ihartwig/mate-net-monitor/pcb/gerber/mate-net-monitor-Fab.pdf

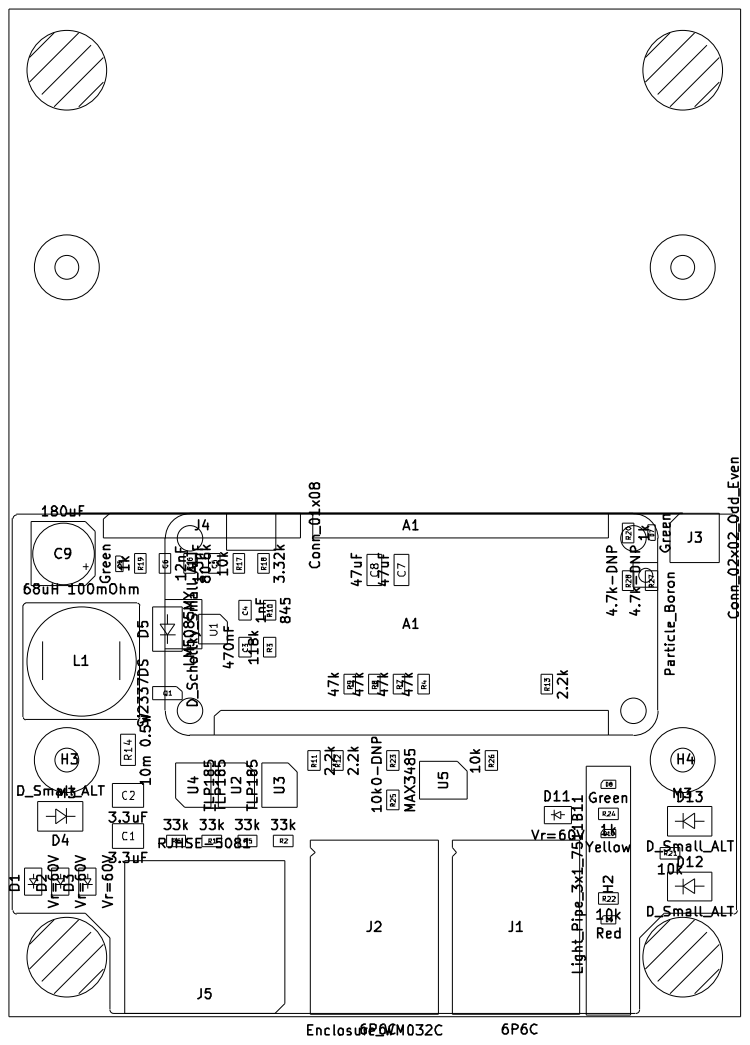
[picture p21: page 1]
